Schlaimwendla/ascenta/diplomarbeit/chapters/99_acknowledgements.tex

\chapter*{Danksagung}
\addcontentsline{toc}{chapter}{Danksagung}
An dieser Stelle bedanken wir uns bei allen Personen, die zum Gelingen dieser Diplomarbeit beigetragen und die Projektphase unterstützt haben.

Ein besonderer Dank gilt unserem Betreuer, Dipl.-Ing. Mario Preishuber, für die fachliche Begleitung sowie die wertvollen Impulse und konstruktiven Rückmeldungen. Die fachliche Freiheit und das entgegengebrachte Vertrauen haben den Erfolg dieses Projekts maßgeblich ermöglicht.

Ebenso danken wir unserem Klassenvorstand, Dr.\ Matthias Grimmer, für die tatkräftige Unterstützung und die Begleitung während der vergangenen fünf Schuljahre. Diese konstante Betreuung bildete den Rahmen für unsere schulische und persönliche Weiterentwicklung.

Ein herzlicher Dank geht zudem an unsere Klassenkameraden für den Zusammenhalt über die gesamte fünfjährige Schulzeit. Der stetige Austausch und die vielfältigen Denkanstöße haben die Erarbeitung von Lösungsansätzen bereichert und die Qualität dieser Arbeit positiv beeinflusst.

Abschließend gilt ein großer Dank unseren Familien und Freunden. Wir schätzen den Rückhalt und die Geduld, die uns während der gesamten Erarbeitungszeit entgegengebracht wurden. Diese Unterstützung bildete das Fundament für die erfolgreiche Fertigstellung dieser Arbeit.
