Schlaimwendla/ascenta/diplomarbeit/chapters/01_introduction.tex

%!TEX root = ../main.tex

\chapter{Einleitung}

\section{Motivation und Ausgangssituation}
Die Orientierung in dynamischen urbanen Räumen, wie etwa Bahnhöfen, stellt für Menschen mit Sehbeeinträchtigung eine komplexe Aufgabe dar. Während taktile Hilfsmittel wie der klassische Langstock Hindernisse in Bodennähe erfassen, bleiben Objekte auf Kopf- oder Rumpfhöhe konzeptionell bedingt außerhalb des Erfassungsbereichs. Bestehende elektronische Systeme nutzen unterschiedliche technologische Ansätze, wobei häufig eine Spezialisierung der Hardware oder eine Anbindung an externe Netzinfrastrukturen im Vordergrund steht.

\section{Problemstellung}
Eine Herausforderung bei mobilen Assistenzsystemen ist die Verarbeitung großer Datenmengen in Echtzeit. Viele aktuelle Lösungen stützen sich auf Cloud-basierte Architekturen, was eine kontinuierliche Datenverbindung voraussetzt. Dies kann die Verwendbarkeit in funkberuhigten Zonen einschränken. Zudem erfordert der Transfer von Bild- und Audiodaten an externe Server eine Berücksichtigung der Datensouveränität.

\section{Zielsetzung}
Das Projekt \glqq Ascenta\grqq\ verfolgt das Ziel, einen Prototyp für ein Assistenzsystem zu entwickeln, das visuelle Daten in akustische Informationen übersetzt. Im Zentrum steht ein technisches Konzept, das durch lokale Datenverarbeitung (Offline-Betrieb) eine Unabhängigkeit von externen Serverstrukturen erreicht. Die Umsetzung erfolgt unter Verwendung von Standardkomponenten, um die Machbarkeit einer dezentralen Architektur zu demonstrieren.

\section{Lösungsansatz und Kernidee}
Das System nutzt eine dezentrale \glqq Split-Brain\grqq-Architektur. Dabei agiert die Brille (Arduino Nicla Vision) als Sensoreinheit für die lokale Objekterkennung (Edge-AI). Die weiterführende Logik und die Sprachverarbeitung werden auf das Smartphone des Nutzers ausgelagert, wobei die Kommunikation über ein lokales WiFi-Protokoll erfolgt. Dieser Ansatz verteilt die Rechenlast und nutzt die Prozessorleistung des Mobilgeräts für die Spracherkennung mittels Vosk.
