Schlaimwendla/ascenta/diplomarbeit/chapters/02_use_cases.tex

% !TEX root = ../main.tex

\chapter{Anwendungsfälle}
\label{ch:02_use_cases}

Um die funktionalen Anforderungen an das Assistenzsystem \glqq Ascenta\grqq\ zu definieren, werden im Folgenden konkrete Anwendungsszenarien beschrieben. Diese Szenarien repräsentieren alltägliche Herausforderungen von stark sehbeeinträchtigten oder blinden Personen, die durch das System gelöst werden. Gemäß dem aktuellen Entwicklungsstand fokussieren sich die Anwendungsfälle auf die Erkennung von Personen im direkten Umfeld, die Distanzabschätzung sowie die auditive Interaktion.

\section{Anwendungsfall A: Kollisionsvermeidung mit Personen}

\subsection{Ausgangssituation}
Ein Nutzer bewegt sich mit einem regulären Langstock durch einen öffentlichen Raum, beispielsweise ein Foyer oder einen Gehweg. Während der Langstock Bodenhindernisse (wie Treppenstufen oder Bordsteinkanten) zuverlässig ertastet, registriert er keine stillstehenden oder sich nähernden Personen auf Körper- oder Kopfhöhe, bevor es zu einem physischen Kontakt kommt.

\subsection{Systemverhalten}
Die smarte Brille erfasst kontinuierlich das Sichtfeld des Nutzers. Sobald eine Person in den unmittelbaren Weg des Nutzers tritt, erkennt das System diese Gefahrenquelle und schätzt die Entfernung ab. Unterschreitet die Person einen kritischen Abstand (beispielsweise einen Meter), reagiert das System sofort. Der Nutzer erhält in Echtzeit ein diskretes, akustisches Warnsignal über sein Smartphone. Dadurch wird er frühzeitig auf das Hindernis aufmerksam gemacht und kann rechtzeitig ausweichen, ohne dass es zu einem physischen Kontakt kommt.

\section{Anwendungsfall B: Kontextbezogene Umgebungsabfrage per Sprachbefehl}

\subsection{Ausgangssituation}
Der Nutzer befindet sich in einer Warteschlange oder an einem Haltepunkt (z.\,B. einer Bushaltestelle) und möchte wissen, ob sich eine Person direkt vor ihm befindet, um entsprechend aufrücken oder Abstand halten zu können. Ein weites Ausschwenken des Langstocks ist in dieser Situation unerwünscht, da es andere Personen stören oder irritieren könnte.

\subsection{Systemverhalten}
Anstatt die Umgebung physisch abzutasten, nutzt der Anwender die integrierte Sprachsteuerung. Er aktiviert das System durch einen einfachen Doppeltipp an der Brille und fragt beispielsweise: \glqq Befindet sich jemand vor mir?\grqq. Das System verarbeitet diese Sprachanfrage lokal und gleicht sie mit der aktuellen visuellen Umgebung ab. Innerhalb von Sekundenbruchteilen erhält der Nutzer über sein Smartphone eine gesprochene Antwort, wie etwa: \glqq Person in anderthalb Metern Entfernung erkannt.\grqq\ Dadurch gewinnt der Nutzer ohne stigmatisierende Bewegungen ein präzises Verständnis seiner unmittelbaren sozialen Umgebung.
