Schlaimwendla/ascenta/diplomarbeit/chapters/07_conclusion.tex

% !TEX root = ../main.tex
\chapter{Fazit}

Zusammenfassend belegt Ascenta erfolgreich die technische Machbarkeit eines vollständig offline-fähigen, tragbaren Assistenzsystems für Menschen mit Sehbehinderung. Durch die intelligente Aufteilung der Rechenlast zwischen der ressourceneffizienten Edge-AI auf dem Nicla Vision und einem Smartphone konnten kritische Latenzen minimiert und strenge Hardware-Limitierungen überwunden werden. Ein sicheres, modulares Energiemanagement sowie gezielte Software-Optimierungen – wie der Einsatz quantisierter FOMO-Modelle und stabiler TCP-Verbindungen – garantieren dabei die nötige Alltagstauglichkeit in einem kompakten Brillengestell. Auch wenn die Anzahl der simultan erkennbaren Objektklassen derzeit noch durch die Mikrocontroller-Hardware begrenzt ist, schafft diese Architektur eine robuste, barrierefreie Grundlage für zukünftige Iterationen und umfassendere Alltagshilfen.
