Schlaimwendla/ascenta/diplomarbeit/chapters/00_deckblatt.tex

% !TEX root = ../main.tex

\titlehead{%
\begin{minipage}[c]{0.20\linewidth}

\end{minipage}
\begin{minipage}[c]{0.5\linewidth}
\begin{center}
{\bfseries\sffamily\large Höhere technische Bundeslehranstalt\\
und Bundesfachschule\\
{\normalsize im Hermann Fuchs Bundesschulzentrum} }
\end{center}
\end{minipage}
\begin{minipage}[c]{0.2\linewidth}
\hfill 
\end{minipage}\\
}

\title{\vspace{1em}Ascenta - Guiding your Vision}
\subtitle{ {\Large Diplomarbeit}\\[1em]Schulautonomer Schwerpunkt\\ Coding \& AI}

\author{\\[2em] 
\emph{ausgeführt im Schuljahr 2025/2026 von:} \\[1em] 
Liam Vendel, 5AHELS\\[1ex] 
Fabian Lindlbauer, 5AHELS\\[1ex] 
Manuel Zauner, 5AHELS\\[2em]
\emph{Betreuer:} \\[1em]
 Dipl.-Ing. Mario Preishuber
}
\date{\vspace{1\baselineskip}Braunau am Inn, am 06.04.2026}
\singlespacing
\maketitle
\onehalfspacing
