Schlaimwendla/ascenta/diplomarbeit/media/images/Abdeckung v1.png

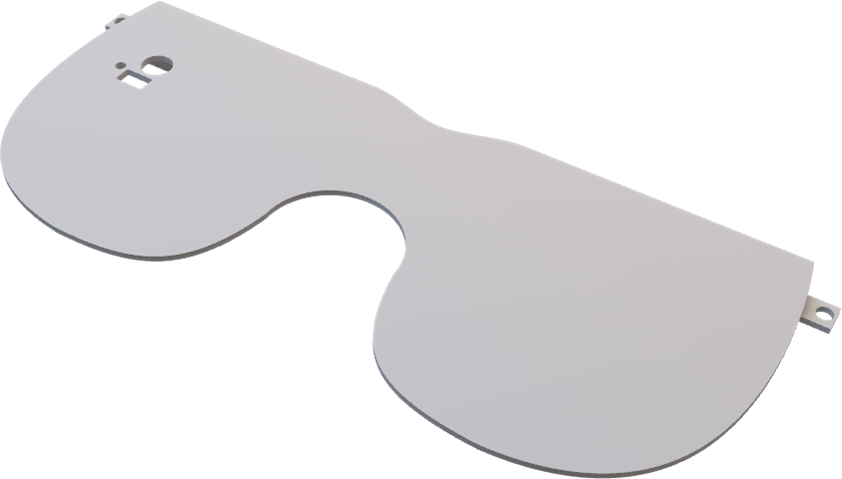
diplomarbeit/media/images/Abdeckung v1.png
