Schlaimwendla/ascenta/diplomarbeit/media/images/akkus_vergleich.png

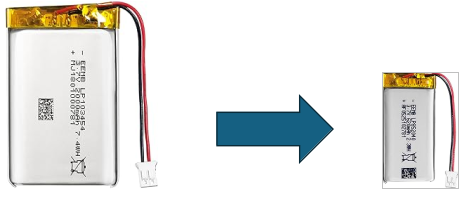
diplomarbeit/media/images/akkus_vergleich.png
