Schlaimwendla/ascenta/demo/NiclaVision/config.py

import bluetooth

# --- BLE UUIDS ---
NICLA_SERVICE_UUID = bluetooth.UUID("12345678-1234-5678-1234-567890ABCDEF")
DATA_CHAR_UUID     = bluetooth.UUID("12345678-1234-5678-1234-567890ABCDE0")
CMD_SERVICE_UUID   = bluetooth.UUID("80000000-0000-1000-8000-00805f9b34fb")
CMD_CHAR_UUID      = bluetooth.UUID("80000001-0000-1000-8000-00805f9b34fb")

UART_SERVICE_UUID = bluetooth.UUID("6E400001-B5A3-F393-E0A9-E50E24DCCA9E")
UART_TX_UUID      = bluetooth.UUID("6E400003-B5A3-F393-E0A9-E50E24DCCA9E")
UART_RX_UUID      = bluetooth.UUID("6E400002-B5A3-F393-E0A9-E50E24DCCA9E")

# --- AUDIO SETTINGS ---
REC_SECONDS = 3.5
SAMPLE_RATE = 16000
CHANNELS = 1
BYTES_PER_SAMPLE = 2
TOTAL_AUDIO_BYTES = int(SAMPLE_RATE * CHANNELS * BYTES_PER_SAMPLE * REC_SECONDS)
AUDIO_CHUNK_SIZE = 4096
NUM_AUDIO_CHUNKS = (TOTAL_AUDIO_BYTES // AUDIO_CHUNK_SIZE) + 1

# --- IMAGE CONSTANTS ---
IMAGE_START_SEQ = b'\xAA\xBB\xCC\xDD'
IMAGE_END_SEQ   = b'\xDD\xCC\xBB\xAA'
